edmugu/arduino_adjustable_power_supply/documentation/snippets/analog_board_back.PNG

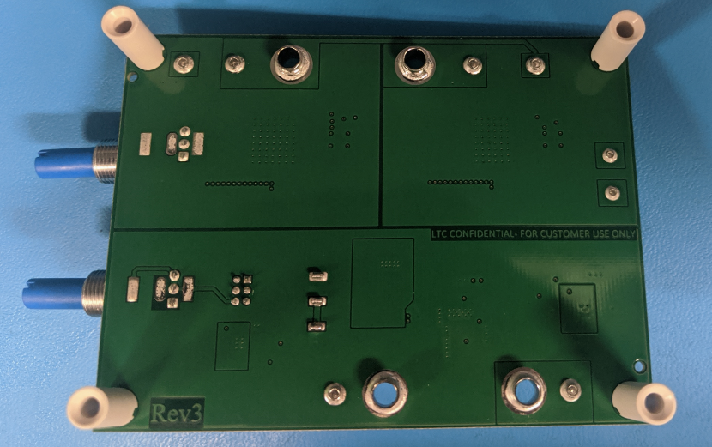
documentation/snippets/analog_board_back.PNG
