edmugu/arduino_adjustable_power_supply/documentation/snippets/below_1V2.PNG

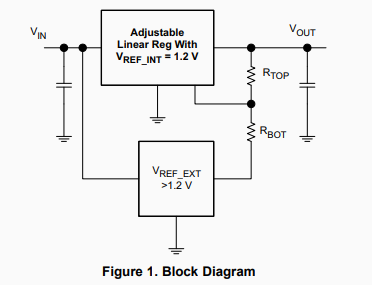
documentation/snippets/below_1V2.PNG
