edmugu/arduino_adjustable_power_supply/documentation/snippets/INA199.PNG

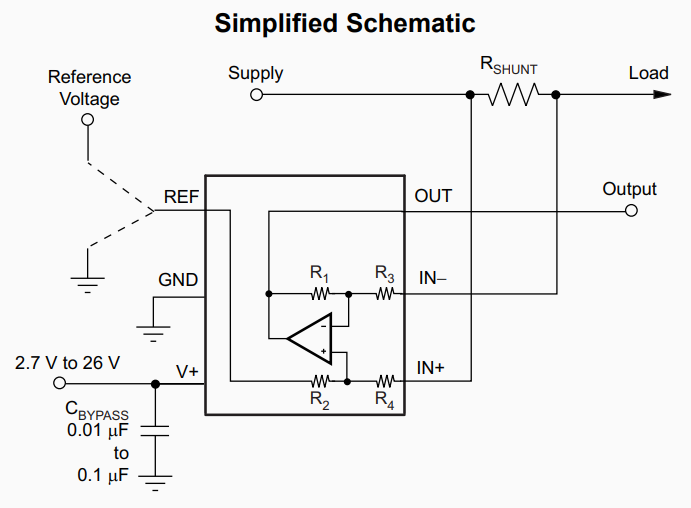
documentation/snippets/INA199.PNG
