edmugu/arduino_adjustable_power_supply/documentation/snippets/lmr64010_duty_cycle.PNG

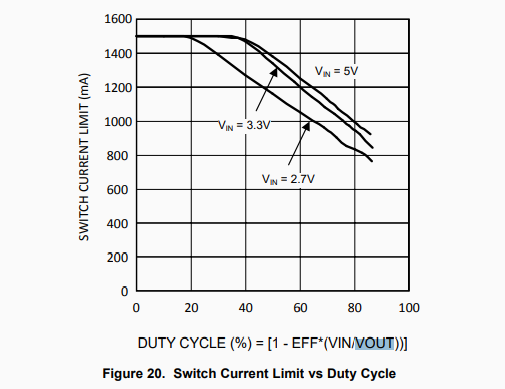
documentation/snippets/lmr64010_duty_cycle.PNG
