edmugu/arduino_adjustable_power_supply/documentation/snippets/LTC4367_settings.PNG

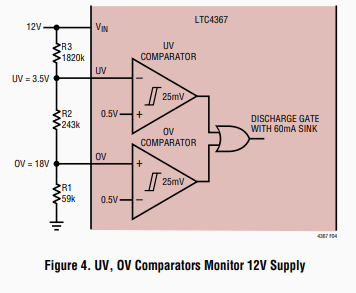
documentation/snippets/LTC4367_settings.PNG
