edmugu/arduino_adjustable_power_supply/Jekyll_page/snips/prototype_board.PNG

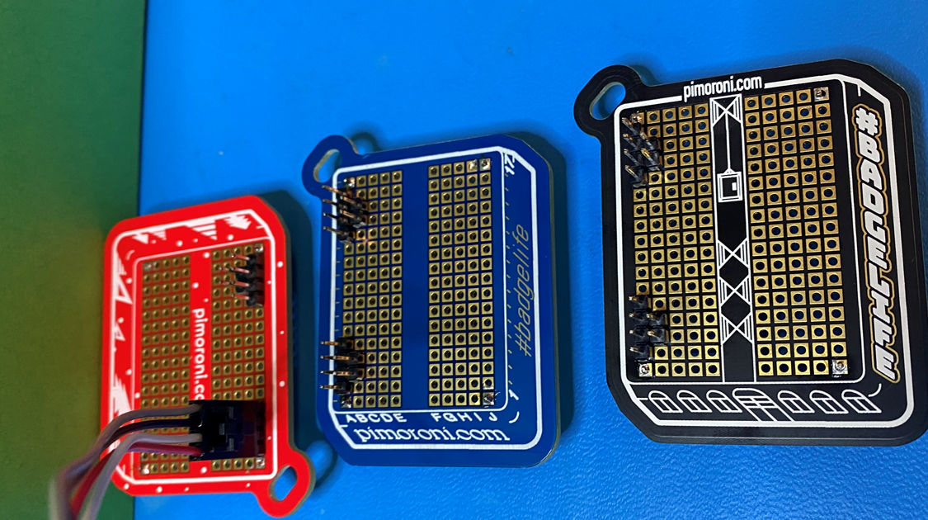
Jekyll_page/snips/prototype_board.PNG
