edmugu/arduino_adjustable_power_supply/Rev_B/Fritzing/Stage_0_bb.png

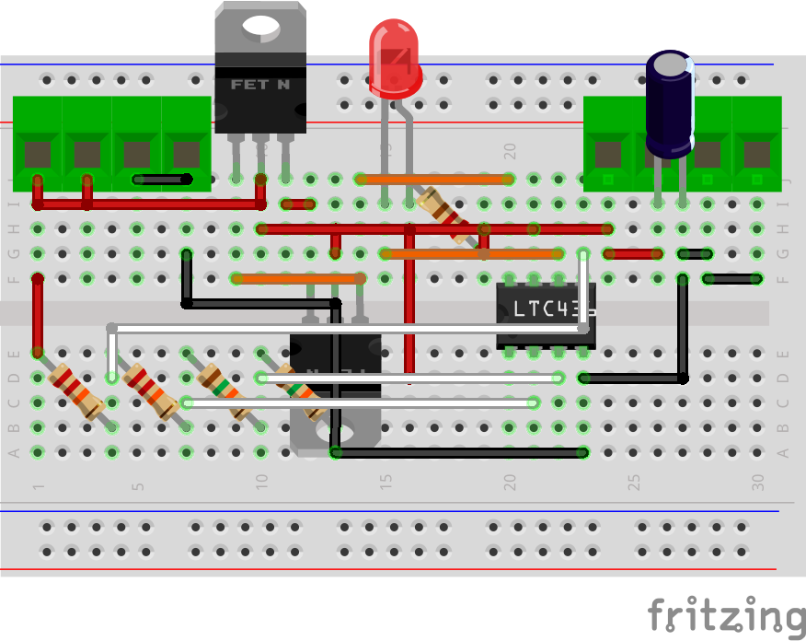
Rev_B/Fritzing/Stage_0_bb.png
