edmugu/arduino_adjustable_power_supply/Rev_B/Fritzing/stage_0_prototype.jpg

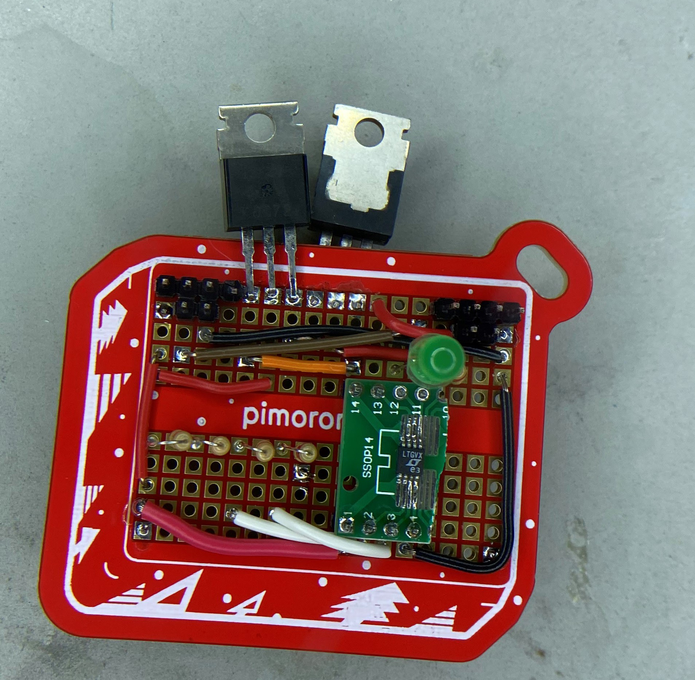
Rev_B/Fritzing/stage_0_prototype.jpg
