edmugu/arduino_adjustable_power_supply/Rev_B/Jekyll_page/snipits/final_stage.jpg

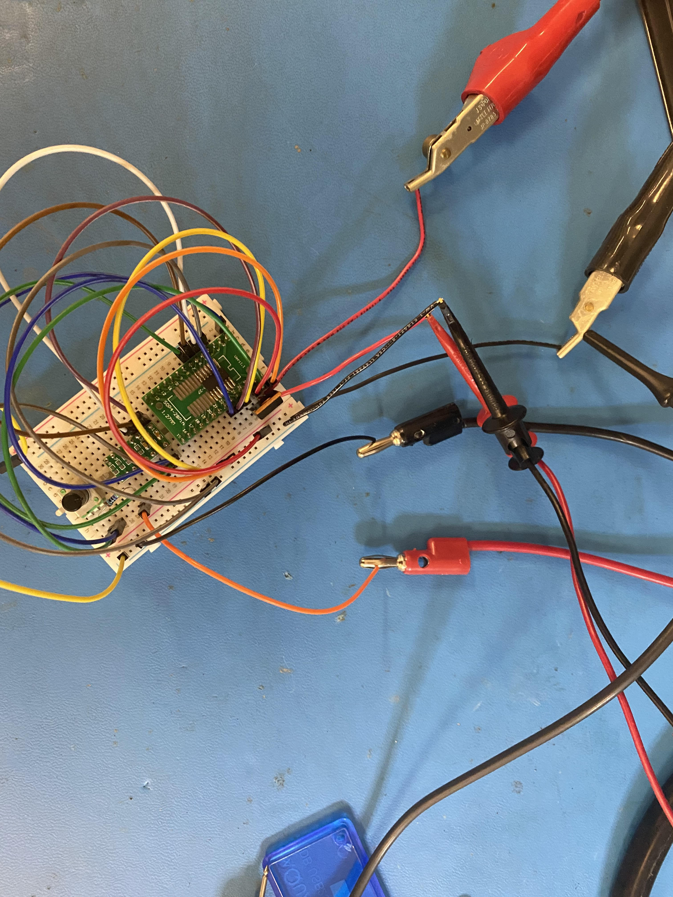
Rev_B/Jekyll_page/snipits/final_stage.jpg
