edmugu/arduino_adjustable_power_supply/Rev_B/Jekyll_page/snipits/first_pcb_draft.PNG

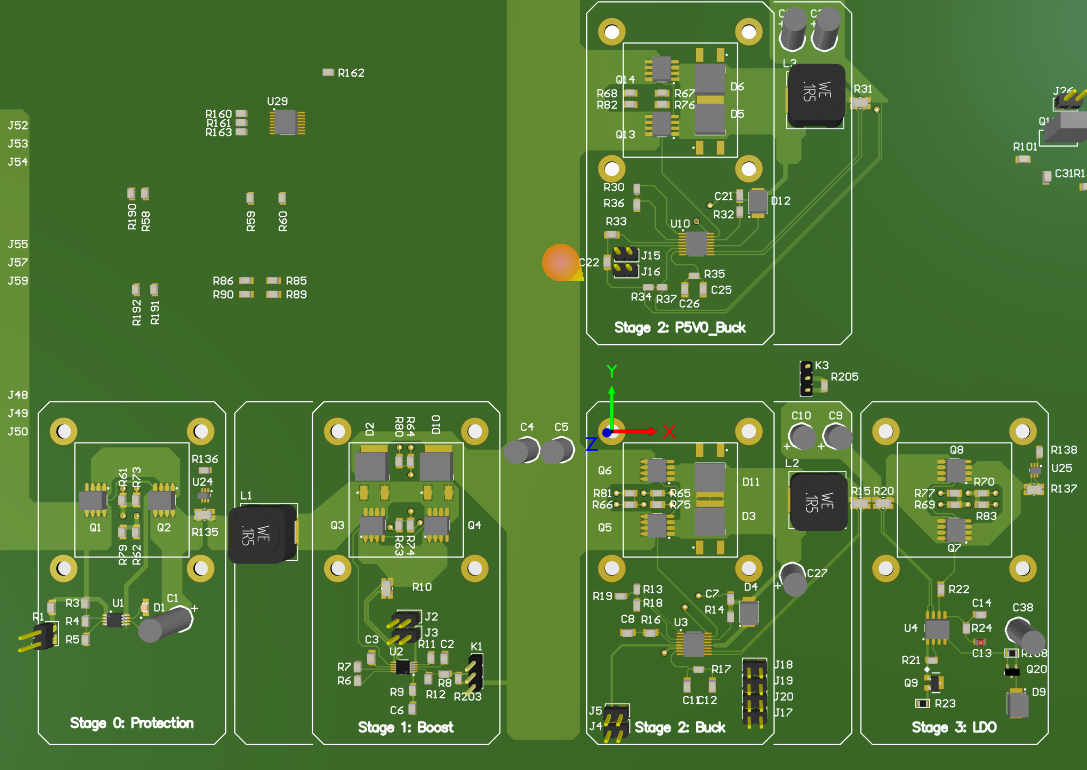
Rev_B/Jekyll_page/snipits/first_pcb_draft.PNG
