edmugu/arduino_adjustable_power_supply/Rev_B/Jekyll_page/snipits/LT1575.PNG

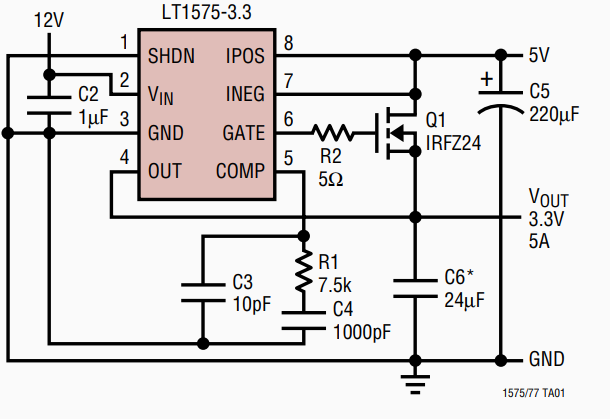
Rev_B/Jekyll_page/snipits/LT1575.PNG
