edmugu/arduino_adjustable_power_supply/Rev_B/Jekyll_page/snipits/pcb_layer_bot.png

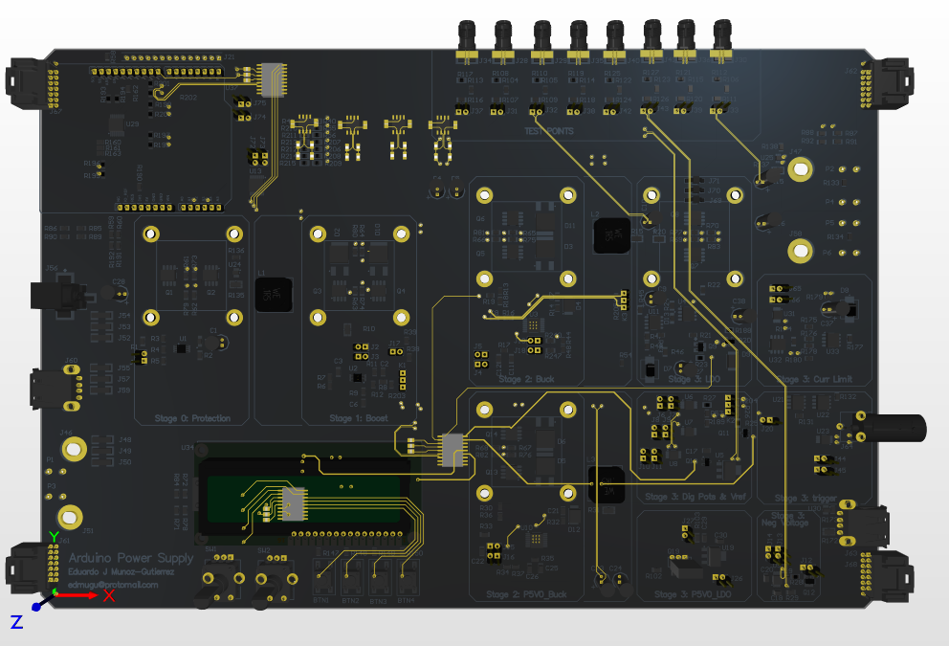
Rev_B/Jekyll_page/snipits/pcb_layer_bot.png
