edmugu/arduino_adjustable_power_supply/Rev_B/Jekyll_page/snipits/pcb_layer_sgn1.png

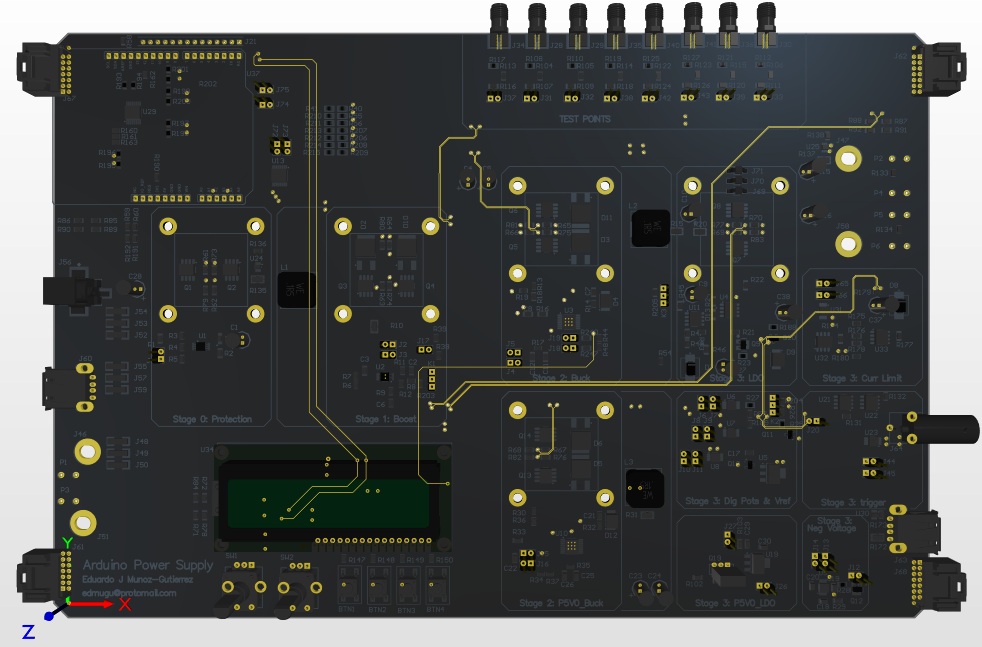
Rev_B/Jekyll_page/snipits/pcb_layer_sgn1.png
