edmugu/arduino_adjustable_power_supply/Rev_B/Jekyll_page/snipits/pcb_scope_vbuck.PNG

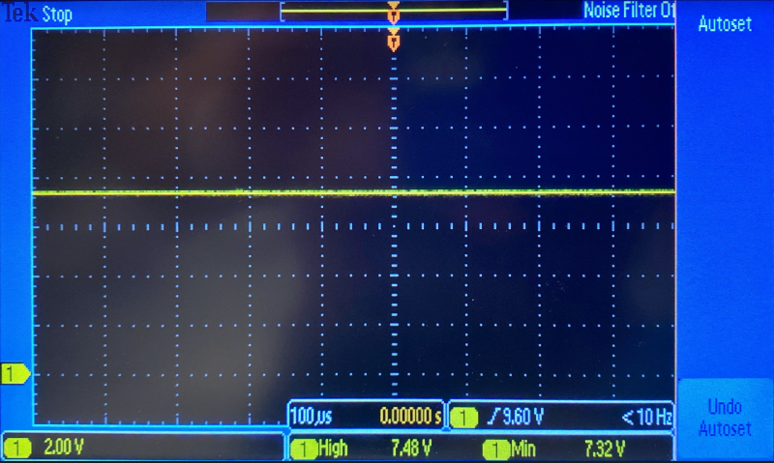
Rev_B/Jekyll_page/snipits/pcb_scope_vbuck.PNG
