edmugu/arduino_adjustable_power_supply/Rev_B/Jekyll_page/snipits/picture_encoder.PNG

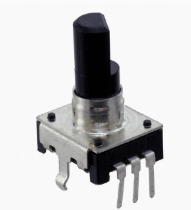
Rev_B/Jekyll_page/snipits/picture_encoder.PNG
