edmugu/arduino_adjustable_power_supply/Rev_B/Jekyll_page/snipits/stage3a.PNG

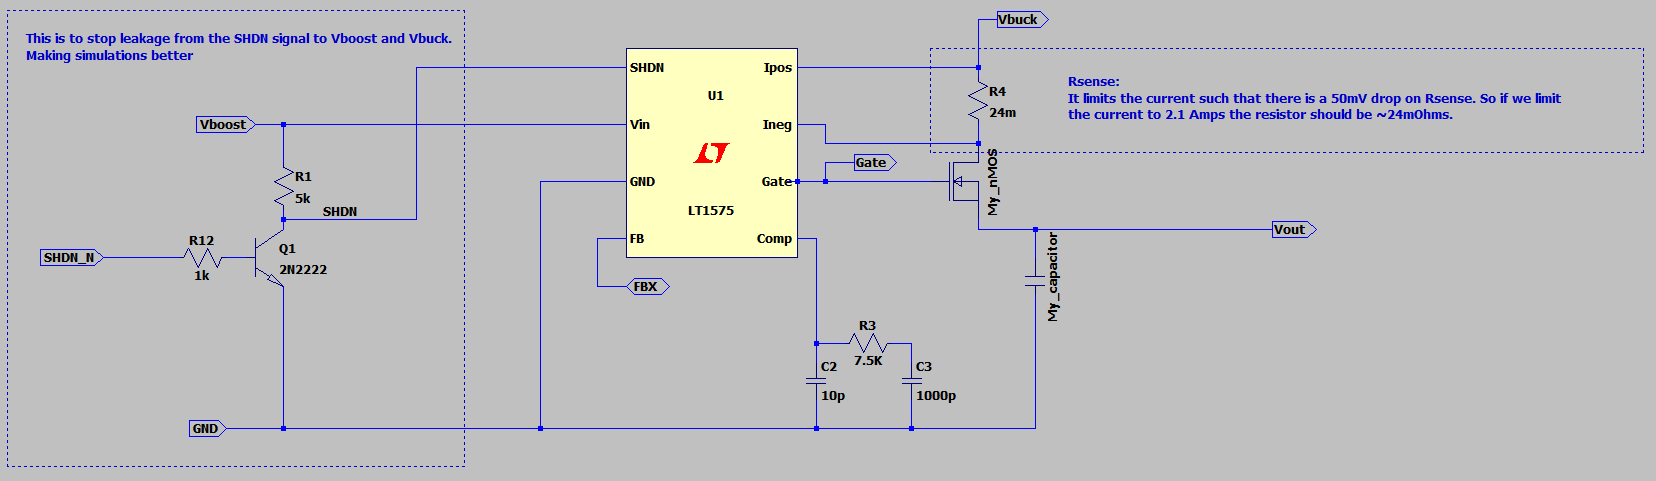
Rev_B/Jekyll_page/snipits/stage3a.PNG
