edmugu/arduino_adjustable_power_supply/Rev_B/Jekyll_page/snipits/stage3b.PNG

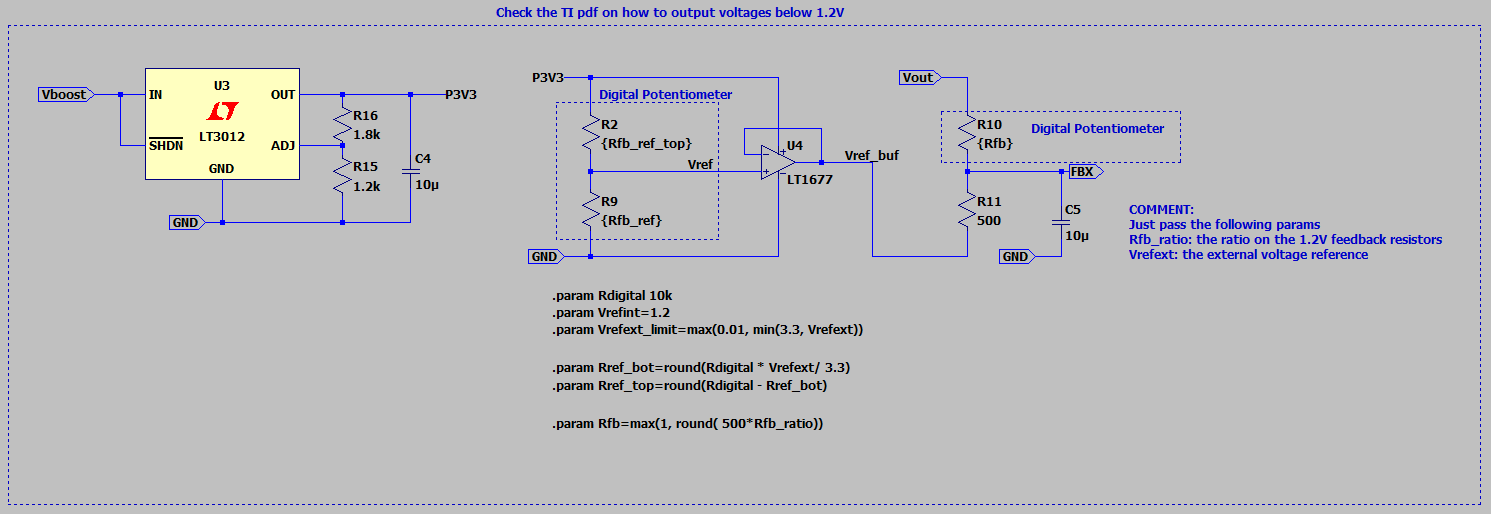
Rev_B/Jekyll_page/snipits/stage3b.PNG
