edmugu/arduino_adjustable_power_supply/Rev_B/Simulation/snip-it/stage_1_max_current.PNG

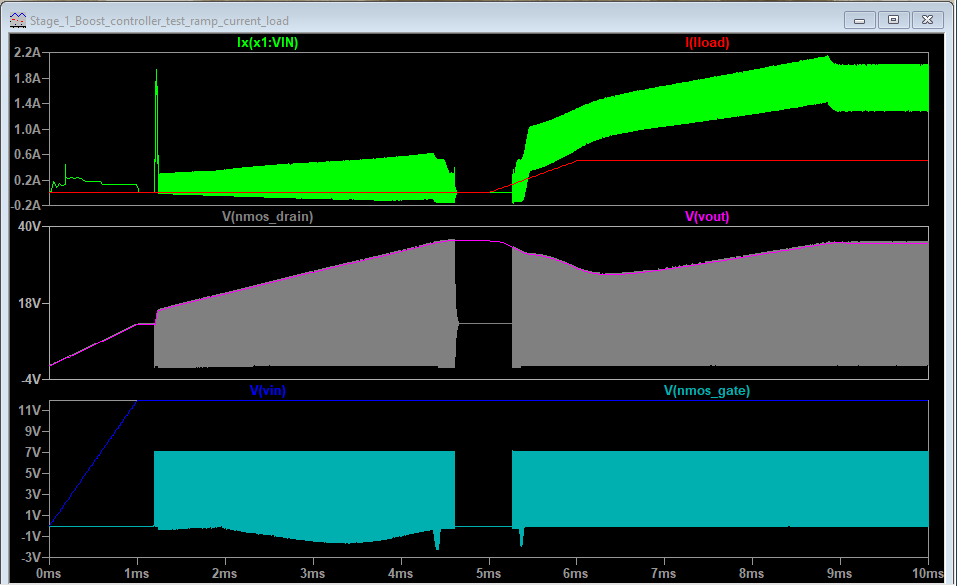
Rev_B/Simulation/snip-it/stage_1_max_current.PNG
