edmugu/arduino_adjustable_power_supply/Rev_B/Simulation/chirp_generator_test.asc

R1: res; 50
X1: chirp_generator
Named nets: 0, Vchirp
.param chirp_ts=0 chirp_te=10m chirp_fs=1k chirp_fe=100k chirp_amp=10m
.tran 0 10m 0 1u startup
