edmugu/arduino_adjustable_power_supply/Rev_B/Simulation/Stage_2_active_feedback_test_inj_transformer.asc

R1: res; 10k
V1: voltage; 32
V2: voltage; PULSE(0 5 8m 1u 0 25 30 10)
X1: Stage_2_active_feedback
X2: Stage_2_Buck_controller
X3: Stage_3_Regulator_controller
X4: chirp_generator
X5: inj_transformer
Named nets: 0, P36V0, Vbuck, Vreg, Vfb, Vref, reg_fbx, S1, Vchirp, Vinj
.tran 0 {chirp_te} 0 1u startup
.param Rfb_ratio=10 Vrefext=0
.param Vrefint=0 Vwanted=Vrefint*(1+Rfb_ratio)-Rfb_ratio*Vrefext
.param chirp_Fs=1k chirp_Fe=100k chirp_te=100m chirp_ts=20m chirp_amp=100m
