edmugu/arduino_adjustable_power_supply/Rev_B/Simulation/Stage_2_active_feedback_test_resistor_load.asc

R1: res; 10k
V1: voltage; {Vwanted + 2}
V2: voltage; PULSE(0 5 8m 1u 0 25 30 10)
X1: Stage_2_active_feedback
X2: Stage_2_Buck_controller
X3: Stage_3_Regulator_controller
Named nets: 0, P36V0, Vbuck, Vreg, Vfb, Vref, reg_fbx, S1
.tran 3000m startup
.param Vin=8 Ioutmax=2.1 Routmin=5/Ioutmax
.param Rfb_ratio=1 Vrefext=0
.param Vrefint=1.2 Vwanted=Vrefint*(1+Rfb_ratio)-Rfb_ratio*Vrefext
