edmugu/arduino_adjustable_power_supply/Rev_B/Simulation/Stage_3_Regulator_controller_test_inj_transformer.asc

I1: current; PULSE(0 2.1 5m 1m 0 8m 10m 10)
R1: res; 50
V1: voltage; PULSE(36 0 5m 5m 0 0 100m 1)
V2: voltage; 36
V3: voltage; ""; AC 1 0
X1: Stage_3_Regulator_controller
X2: inj_transformer
Named nets: 0, Vin, Vout, Gate, FBX, Vpower
.ac dec 1k 1 100k
.param Rfb_ratio=1 Vrefext=0
.param Vrefint=1.2 Vwanted=Vrefint*(1+Rfb_ratio)-Rfb_ratio*Vrefext
