edmugu/arduino_adjustable_power_supply/Rev_B/Simulation/Stage_2_Buck_controller_test_inj_transformer.asc

R1: res; {Routmin}
R2: res; 50
V1: voltage; PULSE(0 {Vin} 0 1m 0 100m 101m 1)
V2: voltage; AC 1 0
X1: Stage_2_Buck_controller
X2: inj_transformer
Named nets: 0, Vin, Vout, TG, FBX, Vinj
.ac dec 1k 1 100k
.param Vin=8 Ioutmax=2.1 Routmin=5/Ioutmax
