edmugu/arduino_adjustable_power_supply/Rev_B/Simulation/Stage_1_Boost_controller_test_inj_transformer.asc

R1: res; {Routmin}
R2: res; 50
V1: voltage; PULSE(0 {Vin} 0 1m 0 100m 101m 1)
V2: voltage; ""; AC 1 0
X1: Stage_1_Boost_controller
X2: inj_transformer
Named nets: 0, Vin, Vout, nMOS_drain, nMOS_gate, nMOS_source, FBX, Vinj
.param Vin=10 Iinmax=2.1 Vinpower=Vin*Iinmax Ioutmax=Vinpower/36 Routmin=36/Ioutmax
.ac dec 1K 1 100K
