edmugu/arduino_adjustable_power_supply/Rev_B/Simulation/power_filter_designs.asc

C1: cap; 10µ
C2: cap; 10µ
C3: cap; 10µ
C4: cap; 10µ
C5: cap; 10µ
C6: cap; 10µ
C7: cap; 10µ
C8: cap; 10p
L1: ind; 100µ
L2: ind; 100µ
Q1: npn; 2N2222
Q2: npn; 2N2222
Q3: npn; 2N2222
Q4: npn; 2N2222
R1: res; 100
R2: res; 20
R3: res; 20
R4: res; 20
R5: res; 20
R6: res; 1k
R7: res; 1k
R8: res; 66k
R9: res; 1k
U1: LT3088
V1: voltage; SINE(5 .25 100k 0 0 0)
Named nets: 0, Vactive1, Vactive2, Vpassive, Vactive1b, Vu, vin
.tran 100m
