edmugu/arduino_adjustable_power_supply/Rev_B/Simulation/Stage_3_Regulator_controller_test_Vout_below_P1V2.asc

R1: res; 1k
V1: voltage; SINE({Vwanted + 0.5} .25 1k 0 0 0 1k)
V2: voltage; {Vwanted + 2}
X1: Stage_3_Regulator_controller
Named nets: 0, Vin, Vout, Gate, FBX, Vpower
.tran 0 1 0 startup
.param Rfb_ratio=1 Vrefext=0
.param Vrefint=1.2 Vwanted=Vrefint*(1+Rfb_ratio)-Rfb_ratio*Vrefext
