edmugu/arduino_adjustable_power_supply/Rev_B/Simulation/Stage_3_Regulator_controller_test_resistor_load.asc

R1: res; 1k
V1: voltage; SINE(10 1 1k 0 0 0 100)
V2: voltage; SINE(12 0.1 1000 0 0 0 100)
X1: Stage_3_Regulator_controller
Named nets: 0, Vbuck, Vout, Gate, FBX, Vboost
.tran 0 100m 0
.param Rfb_ratio=1 Vrefext=0.01
