edmugu/arduino_adjustable_power_supply/Rev_B/Simulation/Stage_3_Regulator_controller_test_resistor_load_max_current.asc

R1: res; {Routmin}
V1: voltage; PULSE(0 {Vboost} 0 1m 0 100m 101m 1)
V2: voltage; SINE({Vbuck} 0.1 1000 0 0 0 100)
X1: Stage_3_Regulator_controller; Vextfb=0 Vfb_ratio=10
Named nets: 0, Vbuck, Vout, Gate, FBX, Vboost
.tran 0 100m 5m startup uic
.param Vwanted=18 Vboost=3+Vwanted Vbuck=0.1+Vwanted
.param Ioutmax=2.1 Routmin=Vwanted/Ioutmax
