edmugu/arduino_adjustable_power_supply/Rev_B/Simulation/Stage_2_Buck_controller_test_resistor_load_max_current.asc

R1: res; {Routmin}
V1: voltage; PULSE(0 {Vin} 0 1m 0 100m 101m 1)
X1: Stage_2_Buck_controller
Named nets: 0, Vin, Vout, TG, FBX
.tran 0 11m 10m startup
.param Vin=8 Ioutmax=2.1 Routmin=5/Ioutmax
