edmugu/arduino_adjustable_power_supply/Rev_B/Simulation/Stage_3_Regulator_controller_test_resistor_load_max_current_stepped.asc

R1: res; {Routmin}
V1: voltage; PULSE(0 {Vbuck} 0 1m 0 1 1 1)
V2: voltage; SINE({Vboost} 0.1 1000 0 0 0 10000)
X1: Stage_3_Regulator_controller
Named nets: 0, Vin, Vout, Gate, FBX, Vpower
.tran 0 200m 0 startup
.param Vfb_ref=0.2
.param Vboost 3+Vwanted
.param Vbuck=0.5+Vwanted
.param Ioutmax=2.1 Routmin=Vwanted/Ioutmax
.step param Vwanted LIST 0.5 1 3.3 5 12 20
.meas Voutavg AVG abs(V(Vin)*I(V1))-abs(V(Vout)*I(R1))
