edmugu/arduino_adjustable_power_supply/Rev_B/Simulation/Current_sense_test_current_load.asc

I1: current; PULSE(0 1 3m 1m 0 6m 10m 10)
R1: res; 0.020
V1: voltage; PULSE(0 20 0 1m 0 9m 10m 10)
X1: Current_sense
Named nets: Vin, Vsense_n, 0, Vout
.tran 10m startup
