edmugu/arduino_adjustable_power_supply/Rev_B/Simulation/My_nMOS_test_current.asc

I1: current; 2.1
V1: voltage; SINE(21 1 1k 0 0 0 100)
V2: voltage; PULSE(0 21 0 2m 0 8m 10m 10)
X1: My_NMOS
Named nets: 0, Vout, Vbuck, Vgate
.tran 0 10m 5m startup
