edmugu/arduino_adjustable_power_supply/Rev_B/Simulation/Stage_0_Reverse_voltage_protection_test_ramp_input.asc

I1: current; PULSE(-10 10 0 1 0 0 0 10)
R1: res; 100
R2: res; 1000
V1: voltage; 10
X2: Stage_0_Reverse_Voltage_Protection
Named nets: 0, Vin, Vout, fault_n
.tran 1
