edmugu/arduino_adjustable_power_supply/Rev_B/Simulation/Stage_0_Reverse_voltage_protection_test_reverse_voltage.asc

R1: res; 100; pwr=100
R2: res; 1000
V1: voltage; -10
X2: Stage_0_Reverse_Voltage_Protection
Named nets: 0, Vin, Vout, fault_n
.tran 10m
