edmugu/arduino_adjustable_power_supply/Rev_B/Simulation/Stage_0_Reverse_voltage_protection_test_typical_load.asc

R1: res; 12; pwr=100
V1: voltage; PULSE(0 12 1m 1m 0 9m 10m 10)
V2: voltage; 12
X2: Stage_0_Reverse_Voltage_Protection
Named nets: 0, Vin, Vout, fault_n
.tran 0 10m 4m
.meas heat AVG Ix(x2:Vin)*V(Vin)+Ix(x2:Vout)*V(Vout)
