edmugu/arduino_adjustable_power_supply/Rev_B/Simulation/Stage_0_Reverse_voltage_protection_test_typical_load_stepped.asc

R1: res; {Rx}; pwr=100
V1: voltage; PULSE(0 12 0 1m 0 9m 10m 10)
V2: voltage; {Vx}
X2: Stage_0_Reverse_Voltage_Protection
Named nets: 0, Vin, Vout, fault_n
.tran 0 10m 5m
.meas Pin AVG V(Vin)*Ix(x2:Vin)
.meas Pout AVG -V(Vout)*Ix(x2:Vout)
.meas Eff PARAM 100*Pout/Pin
.step param Vx 3 20 1
.param Rx Vx*Vx/12
.meas IR MAX I(R1)
.meas PR PARAM Rx*IR*IR
.meas Heat PARAM Pin - Pout
