edmugu/arduino_adjustable_power_supply/Rev_B/Simulation/Stage_1_Boost_controller_test_ramp_current_load.asc

Iload: current; PULSE(0 0.5 5m 1m 0 5m 10m 1)
V1: voltage; PULSE(0 12 0 1m 0 100m 101m 1)
X1: Stage_1_Boost_controller
Named nets: 0, Vin, Vout, nMOS_drain, nMOS_gate, nMOS_source, FBX
.tran 10m
