edmugu/arduino_adjustable_power_supply/Rev_B/Simulation/Stage_1_Boost_controller_test_resistor_load.asc

R1: res; 1k
V1: voltage; PULSE(0 10 0 1m 0 100m 101m 1)
X1: Stage_1_Boost_controller
Named nets: 0, Vin, Vout, nMOS_drain, nMOS_gate, nMOS_source, FBX
.tran 10m
