edmugu/arduino_adjustable_power_supply/Rev_B/Simulation/Stage_2_Buck_controller_test_current_load.asc

R1: res; 1k
V1: voltage; PULSE(0 36 0 1m 0 100m 101m 1)
X1: Stage_2_Buck_controller
Named nets: 0, Vin, Vout, Gate, FBX
.tran 20m startup
