edmugu/arduino_adjustable_power_supply/Rev_B/Simulation/Stage_3_Regulator_controller_test_current_load.asc

I1: current; PULSE(0 2.1 5m 1m 0 8m 10m 10)
V1: voltage; PULSE(36 0 5m 5m 0 0 100m 1)
V2: voltage; 36
X1: Stage_3_Regulator_controller
Named nets: 0, Vin, Vout, Gate, FBX, Vpower
.tran 10m startup
.param Vfb_ref=0 Vwanted=12
