edmugu/arduino_adjustable_power_supply/Rev_B/Simulation/Stage_4_Reverse_current_protection_test_resistor_load.asc

R1: res; 20m
R2: res; 5
V1: voltage; 36
V2: voltage; 8
V3: voltage; 5
X1: Stage_4_Reverse_current_protection
Named nets: Vsense, Vreg, Vbuck, Vboost, Vout, 0
.tran 10m startup
