edmugu/arduino_adjustable_power_supply/Rev_B/Simulation/Stage_4_Reverse_current_protection_test_reverse_current.asc

R1: res; 20m
R2: res; 10
V1: voltage; 36
V2: voltage; 8
V3: voltage; 5
V4: voltage; {Vload}
X1: Stage_4_Reverse_current_protection
Named nets: Vsense, Vreg, Vbuck, Vboost, Vout, 0, Vgate, Vin
.tran 0 10m 1m startup
.meas resistance  AVG (V(vin)-V(vout))/Ix(x1:Vout)
.step param Vload list 0 3 5 6 7 8 9 36
.meas Imax MAX Ix(x1:VOUT)
