edmugu/arduino_adjustable_power_supply/Rev_B/Simulation/chirp_generator.asc

B1: bv; V = chirp_amp*u(time - chirp_ts)*sin(6.283*(chirp_Fs+(chirp_Fe-chirp_Fs)/(chirp_te - chirp_ts)*time/2)*time)
R1: res; 10m
Named nets: 0, Vchirp
The following parameters are needed:
chirp_Fs = Frequency Start
chirp_Fe = Frequency End
chirp_ts = Time start
chirp_te = Time end
chirp_amp = amplitude
