edmugu/arduino_adjustable_power_supply/Rev_B/Simulation/Stage_3_Regulator_controller.asc

C1: cap; 10µ
C2: cap; 10p
C3: cap; 1000p
C4: cap; 10p
M1: nmos; Si7336ADP
M2: nmos; Si7336ADP
Q1: npn; 2N2222
Q2: npn; 2N2222
R1: res; 22k
R2: res; {Rref}
R3: res; 50
R4: res; 24m
R5: res; 20
R6: res; 500
R7: res; 7.5k
R8: res; 50
R9: res; 500
R10: res; {Rfb}
R11: res; 5000
R12: res; 5k
U1: LT1575
U2: LT3088
X1: My_NMOS
X2: My_capacitor
Named nets: Vboost, FBX, GND, Vout, Gate, Vbuck, SHDN_N, SHDN, Vboost_filtered, Vrefext, refext_n, Vinj
Rsense:
It limits the current such that there is a
 50mV drop on Rsense. So if we limit
the current to 2.1 Amps the resistor 
should be ~24mOhms.
Check the TI pdf on how to output voltages below 1.2V
Digital Potentiometer
.param Rref=round(  20k * Vrefext_limit   )
.param Rfb=max(1, round( 5000*Rfb_ratio))
COMMENT: 
Just pass the following params
Rfb_ratio: the ratio on the 1.2V feedback resistors
Vrefext: the external voltage reference
This is to stop leakage from the SHDN signal to Vboost and Vbuck.
Making simulations better
.param Vrefext_limit=max(0.01, min(3.3, Vrefext))
