edmugu/arduino_adjustable_power_supply/Rev_B/Simulation/Stage_2_Buck_controller.asc

C1: cap; 3300p
C2: cap; 680p
C3: cap; 120p
C4: cap; 0.1µ
C6: cap; 1µ
D1: diode
D2: diode
R1: res; 28.7k
R2: res; 1.3k
R3: res; 10
R4: res; 40m
R5: res; 50
R7: res; 200k
R8: res; 15k
R9: res; 12k
R10: res; 38k
U1: LT3724
X1: My_NMOS
X2: My_zenner
X3: My_inductor
X4: My_capacitor
Named nets: Vin, GND, SHDN_N, Vout, Gate, Vcc, FBX, Vinj
