edmugu/arduino_adjustable_power_supply/Rev_B/Simulation/inj_transformer.asc

C1: cap; 10p
L1: ind2; 10µ
L2: ind2; 10µ
Named nets: Vout, Vinj, Osc, 0
K L1 L2 1
