edmugu/arduino_adjustable_power_supply/Rev_B/Simulation/Stage_1_Boost_controller.asc

C1: cap; 0.1µF
C2: cap; 4.7µ
C4: cap; 6.8n
R1: res; 20k
R2: res; 13.7k
R3: res; 21k
R4: res; 1k
R5: res; 31.7m
R6: res; 22k
R7: res; 10k
R8: res; 50
U1: LT3757
X1: My_NMOS
X2: My_zenner
X3: My_inductor
X4: My_capacitor
Named nets: Vin, GND, Vout, SHDN_N, nMOS_drain, nMOS_gate, nMOS_source, FBX, Vinj
Rsense Notes:
    Rsense = 80mV / IL(peak). Note that there should be 20% margin as noted on the data sheet
    Rsense = 80m / (2.1 * 1.2) = 0.080 / 2.52 = 0.0317 Ohms
