edmugu/arduino_adjustable_power_supply/Rev_B/Simulation/Stage_3_MIC5156.asc

U1: LT1677
U2: LT1677
V1: voltage; 35m
V2: voltage; 1.235
Named nets: GND, VDD, D, EA, G, SHDN
