edmugu/arduino_adjustable_power_supply/Rev_B/Simulation/My_capacitor.asc

C1: cap; 100µ
R1: res; 100m
Named nets: R, C
