edmugu/arduino_adjustable_power_supply/Rev_B/Simulation/My_inductor.asc

L1: ind; 10µ
R1: res; 40m
Named nets: l, R
