edmugu/arduino_adjustable_power_supply/Rev_B/Simulation/Stage_2_active_feedback.asc

D1: diode
R1: res; 750
R2: res; 750
R3: res; 1k
R4: res; 1k
U2: LT1677
Named nets: Vin, GND, Vneg, Vpos, Vout_FB, Vref
Vout_FB wants to be at 1.2 volts. So if Vref is below 1.2V - Vdiode it will draw Vout_FB low. 
So
