edmugu/arduino_adjustable_power_supply/Rev_B/Simulation/Arduino_power_supply.asc

I1: current; PULSE(0 2 50m 0 0 50m 100m 1)
R1: res; 20m
R2: res; 20m
V1: voltage; 12
V2: voltage; PULSE(0 5 10m 0 0 90m 100m 1)
V3: voltage; PULSE(0 5 20m 0 0 80m 100m 1)
V4: voltage; PULSE(0 5 30m 0 0 70m 100m 1)
V5: voltage; PULSE(0 5 40m 0 0 60m 100m 1)
V6: voltage; PULSE(0 5 0 1m 0 90m 100m 1)
X2: Current_sense
X3: Stage_1_Boost_controller
X4: Stage_2_Dual_buck_controller
X5: Stage_2_active_feedback
X6: Stage_3_Digital_feedback; Vfb_ref=0 Vwanted=15
X17: Stage_3_Regulator_controller
X18: Stage_4_Reverse_current_protection
X19: Current_sense
Named nets: 0, P5V0, Vboost, Vbuck, Vreg, Vfb, Vout, Vin, VReg, Iin, Iout, S1, S2, S3, S4, S0
.tran 0 100m 0 startup
