edmugu/arduino_adjustable_power_supply/Rev_B/Simulation/buffer_with_floating_output.asc

U1: LT1677
U2: ADG1209
Named nets: Vbuffered, Vin, GND, output_en, Vunbuffered
