edmugu/arduino_adjustable_power_supply/Rev_B/Simulation/Current_sense.asc

R1: res; 20
R2: res; 1k
R3: res; 20
U1: LTC6102
Named nets: Sense_p, Sense_n, Vin, Vout, GND
